Xoma163/k1c-upgrades/config/k1c #2/printer.cfg

# Modified by Simple AF 2026-03-28_13-22-50

[include homing.cfg]

[include internal_macros.cfg]

[include useful_macros.cfg]

[include belts_calibration.cfg]

[include start_end.cfg]

[include Line_Purge.cfg]

[include Smart_Park.cfg]

[include fan_control.cfg]

[include client.cfg]

[include quickstart.cfg]

[include eddyng.cfg]

[include eddyng_macro.cfg]

[mcu]
serial: /dev/ttyS7
baud: 230400
restart_method: command

[mcu nozzle_mcu]
serial: /dev/ttyS1
baud: 230400
restart_method: command

[verify_heater extruder]
[verify_heater heater_bed]
check_gain_time: 120
heating_gain: 1.0
hysteresis: 10

[gcode_arcs]
resolution: 1.0

[stepper_x]
step_pin: PC2
dir_pin: !PB9
enable_pin: !PC3
microsteps: 32
rotation_distance: 40
endstop_pin: tmc2209_stepper_x:virtual_endstop
position_endstop: 229
position_min: -5
position_max: 229
homing_speed: 30
homing_retract_dist:0

[tmc2209 stepper_x]
uart_pin:PA9
interpolate: True
run_current:1.5
sense_resistor: 0.100
stealthchop_threshold: 0
uart_address:3
diag_pin: ^PB12
# driver_IHOLDDELAY: 8
# driver_TPOWERDOWN: 20
# driver_TBL: 1
# driver_TOFF: 1
# driver_HEND: 0
# driver_HSTRT: 7
driver_SGTHRS: 75
# hold_current:1.0

[stepper_y]
step_pin: PB8
dir_pin: !PB7
enable_pin: !PC3
microsteps: 32
rotation_distance: 40
endstop_pin: tmc2209_stepper_y:virtual_endstop
position_endstop: -0.5
position_min: -0.5
position_max: 226
homing_speed: 30
homing_retract_dist:0

[tmc2209 stepper_y]
uart_pin:PA10
interpolate: True
run_current:1.5
sense_resistor: 0.100
stealthchop_threshold: 0
uart_address:3
diag_pin: ^PB13
# driver_IHOLDDELAY: 8
# driver_TPOWERDOWN: 20
# driver_TBL: 1
# driver_TOFF: 1
# driver_HEND: 0
# driver_HSTRT: 7
driver_SGTHRS: 75
# hold_current:1.0

[stepper_z]
step_pin: PB6
dir_pin: !PB5
enable_pin: !PC3
microsteps: 16
rotation_distance:8
gear_ratio: 64:20
endstop_pin: probe:z_virtual_endstop
position_max: 252
position_min: -5
# position_endstop: 0

[tmc2209 stepper_z]
uart_pin: PA11
uart_address: 3
run_current: 0.8
diag_pin: ^PB14
stealthchop_threshold: 0
sense_resistor: 0.100
# driver_IHOLDDELAY: 8
# driver_TPOWERDOWN: 20
# driver_TBL: 1
# driver_TOFF: 1
# driver_HEND: 2
# driver_HSTRT: 2
driver_SGTHRS: 0

[extruder]
max_extrude_only_distance: 1000.0
max_extrude_cross_section: 80
step_pin: nozzle_mcu:PB1
dir_pin: nozzle_mcu:PB0
enable_pin: !nozzle_mcu:PB2
microsteps: 16
rotation_distance: 6.9
nozzle_diameter: 0.400
filament_diameter: 1.750
heater_pin: nozzle_mcu:PB7
sensor_type: EPCOS 100K B57560G104F
sensor_pin: nozzle_mcu:PA0
pressure_advance: 0.04
pressure_advance_smooth_time: 0.040
control: pid
pid_Kp: 25.013
pid_Ki: 2.566
pid_Kd: 60.966
min_temp: 0
max_temp: 320

[tmc2209 extruder]
uart_pin: nozzle_mcu:PB11
tx_pin: nozzle_mcu:PB10

uart_address: 3
run_current: 0.55
sense_resistor: 0.150
stealthchop_threshold: 0
# driver_IHOLDDELAY: 8
# driver_TPOWERDOWN: 20
# driver_TBL: 2
# driver_TOFF: 3
# driver_HEND: 0
# driver_HSTRT: 5

[heater_bed]
heater_pin: PB10
sensor_type: EPCOS 100K B57560G104F
sensor_pin: PC4
control: watermark
min_temp: 0
max_temp: 115

[filament_switch_sensor filament_sensor]
pause_on_runout: false
switch_pin: !PC15
runout_gcode: _ON_FILAMENT_RUNOUT

[output_pin LED]
pin:PB0
pwm: True
cycle_time: 0.010
value: 1

[adxl345]
cs_pin: nozzle_mcu:PA4
spi_speed: 5000000
axes_map: x,-z,y
spi_software_sclk_pin: nozzle_mcu:PA5
spi_software_mosi_pin: nozzle_mcu:PA7
spi_software_miso_pin: nozzle_mcu:PA6

[resonance_tester]
accel_chip: adxl345
accel_per_hz: 75
# min_freq: 30
# max_freq: 100
probe_points:
   110,110,10

[printer]
kinematics: corexy
max_velocity: 600
max_accel: 20000
max_z_velocity: 10
square_corner_velocity: 5.0
# square_corner_max_velocity: 200.0
# max_accel_to_decel: 20000
max_z_accel: 300

[probe_eddy_ng btt_eddy]

[exclude_object]

# custom andrewsha https://pellcorp.github.io/creality-wiki/nozzle_wipe/#purcell-nozzle-wipe
[include advanced_nozzle_cleaner.cfg]

# custom andrewsha (переопределения переменных)
[include custom.cfg]

# custom andrewsha (переопределения макросов)
[include custom_macros.cfg]

#*# <---------------------- SAVE_CONFIG ---------------------->
#*# DO NOT EDIT THIS BLOCK OR BELOW. The contents are auto-generated.
#*#
#*# [bed_mesh default]
#*# version = 1
#*# points =
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
#*# x_count = 20
#*# y_count = 20
#*# mesh_x_pps = 2
#*# mesh_y_pps = 2
#*# algo = bicubic
#*# tension = 0.2
#*# min_x = 10.0
#*# max_x = 204.94
#*# min_y = 10.0
#*# max_y = 209.88000000000005
#*#
#*# [probe_eddy_ng btt_eddy]
#*# calibrated_drive_currents = 16, 17
#*# calibration_version = 5
#*# calibration_16 = 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
#*# calibration_17 = 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
