Xoma163/k1c-upgrades/config/k1c #1/custom.cfg

# ---------- PRINTER.CFG ---------- #

[input_shaper]
shaper_type_x = mzv
shaper_freq_x = 61.6
shaper_type_y = mzv
shaper_freq_y = 56.8

[extruder]
control = pid
pid_kp = 24.618
pid_ki = 2.605
pid_kd = 58.160

[heater_bed]
control = pid
pid_kp = 64.112
pid_ki = 0.708
pid_kd = 1452.141

[filament_switch_sensor DXC]
pause_on_runout: False
switch_pin: !nozzle_mcu:PA10
runout_gcode: FILAMENT_RUNOUT SENSOR=DXC
insert_gcode: FILAMENT_INSERT SENSOR=DXC

# ---------- INITIALIZATION ---------- #

# Этот gcode выполняется после 5 секунд как принтер загрузится
[delayed_gcode startup_code]
initial_duration: 5
gcode:
    # Максимальные ускорения по умолчанию - 5к
    SET_VELOCITY_LIMIT ACCEL=5000
    # Температура в камере не более 40 градусов
    SET_TEMPERATURE_FAN_TARGET TEMPERATURE_FAN=chamber_fan TARGET=40
    # Отключение прогрева стола 10 минут
    SET_PIN PIN=Bed_Warp_Stabilisation VALUE=0
    # Выбор стандартного профиля BED_MESH
    BED_MESH_PROFILE LOAD="default_hot_20x20"

# ---------- EDDYNG.CFG ---------- #

[probe_eddy_ng btt_eddy]
# Я так понял, чтобы он носиком ниже бился (для z-offset)
tap_target_z: -0.350
# z-offset
tap_adjust_z = 0.090
# regular 16
reg_drive_current = 16
# tap 17
tap_drive_current = 17

[bed_mesh]
# Исключение мёртвых зон
# X < 5
faulty_region_1_min: 0,0
# Если поставить 205, то ругнётся на overlap
faulty_region_1_max: 5,204.999
# Кастомные петли двери: 0..8 x 0..5
# Из-за overlap начинаю вторую зону чуть правее X=5
faulty_region_2_min: 5.001,0
faulty_region_2_max: 8,5
# Y > 205
faulty_region_3_min: 0,205
faulty_region_3_max: 220,220

# ---------- START_END.CFG ---------- #

[gcode_macro _START_END_PARAMS]
variable_end_print_keep_bed_heated: False

[gcode_macro _CLIENT_VARIABLE]
# На сколько опускать стол после печати
variable_custom_park_dz: 60
# Где парковать Y ось
variable_park_at_cancel_y: 190
# Сколько филамента вытягивать после печати/отмены в мм
variable_cancel_retract: 10

[gcode_macro _KAMP_Settings]
# Сколько сопло должно выдавить филамента перед началом движения линии в мм
variable_tip_distance: 5.0
# Сколько сопло должно выдавить филамента во время движения в мм
variable_purge_amount: 50

# ---------- USEFUL_MACROS.CFG ---------- #

[gcode_macro LOAD_FILAMENT]
# Сколько филамента должно загружаться при нажатии на кнопку
variable_extrude_len: 200

# ---------- ADVANCED_NOZZLE_CLEANER.CFG ---------- #

[gcode_macro WIPE_NOZZLE]
variable_first_layer_temp: 250

# ---------- CUSTOM ---------- #

[gcode_macro _CUSTOM_ANDREWSHA_SETTINGS]
# Позиция x,y start для начала Line Purge, а также для Smart Park
variable_purge_start_x: 85
variable_purge_start_y: 212
variable_purge_end_x: 35
variable_purge_end_y: 212

# Лимиты bed_mesh
variable_bed_mesh_range_limit: 0.30

gcode:
